FelixWeichselgartner/PiHeld/hardware/cartridge_pcb/simulations/save_shutdown/save_shutdown.asc

C1: cap; 22µ
M1: nmos; 2N7002
M2: nmos; 2N7002
R1: res; 1Meg
R2: res; 10K
R3: res; 10K
S1: sw; SW1
V1: voltage; 3.7; Rser=0.1
V2: voltage; PULSE(0 3.7 0 0 0 30 60 1); Rser=0.1
Named nets: 0
.param vres=1M vcap=22u
.tran 0 90 0 1
.model SW1 SW(Ron=0.001 Roff=10Meg Vt=1.1 Vh=0.1)
