FelixWeichselgartner/PiHeld/software/code/src/datatypes.h

#ifndef DATATYPES_H_
#define DATATYPES_H_

// using those, because microcontrollers might not have char, short etc..
#include <stdint.h>

typedef uint8_t     Byte;
typedef uint16_t    Word;
typedef int8_t      sByte;
typedef int16_t     sWord;

#endif
